MattDarcy/KAUSat-5-Sensor-Sim/raw/KAUsign.png

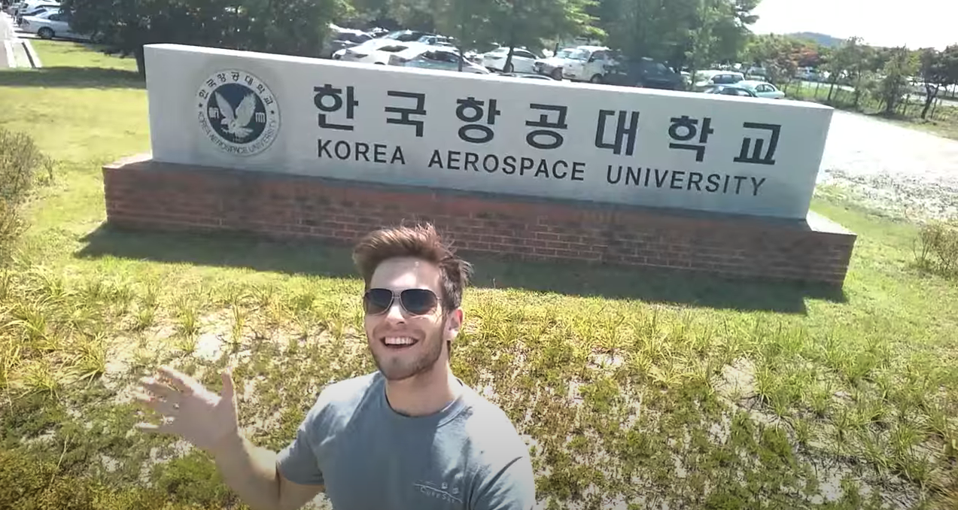
raw/KAUsign.png
