MattDarcy/KAUSat-5-Sensor-Sim/raw/youtubethumb.png

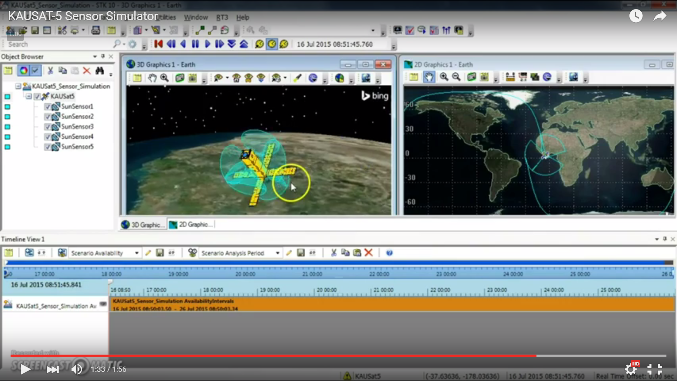
raw/youtubethumb.png
